lvoytek/timechime/src/sprites.c

#include <lvgl.h>

#include "sprites.h"

// I1 format: 2×lv_color32_t palette (blue,green,red,alpha) then pixel rows MSB-first.
// palette[0]=white background, palette[1]=black foreground; bit 1=arrow body.
static const uint8_t sprite_up_data[] = {
	0xFF, 0xFF, 0xFF, 0xFF, 0x00, 0x00, 0x00, 0xFF, // palette: white, black
	0x00, 0x01, 0x80, 0x00,                         // row  0: tip (2px)
	0x00, 0x03, 0xC0, 0x00,                         // row  1
	0x00, 0x07, 0xE0, 0x00,                         // row  2
	0x00, 0x0F, 0xF0, 0x00,                         // row  3
	0x00, 0x1F, 0xF8, 0x00,                         // row  4
	0x00, 0x3F, 0xFC, 0x00,                         // row  5
	0x00, 0x7F, 0xFE, 0x00,                         // row  6
	0x00, 0xFF, 0xFF, 0x00,                         // row  7
	0x01, 0xFF, 0xFF, 0x80,                         // row  8
	0x03, 0xFF, 0xFF, 0xC0,                         // row  9
	0x07, 0xFF, 0xFF, 0xE0,                         // row 10
	0x0F, 0xFF, 0xFF, 0xF0,                         // row 11
	0x1F, 0xFF, 0xFF, 0xF8,                         // row 12
	0x3F, 0xFF, 0xFF, 0xFC,                         // row 13
	0x7F, 0xFF, 0xFF, 0xFE,                         // row 14
	0xFF, 0xFF, 0xFF, 0xFF,                         // row 15: base (32px)
	0x00, 0x0F, 0xF0, 0x00,                         // row 16: stem start (8px)
	0x00, 0x0F, 0xF0, 0x00,                         // row 17
	0x00, 0x0F, 0xF0, 0x00,                         // row 18
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
	0x00, 0x03, 0xC0, 0x00,                         // row 28
	0x00, 0x01, 0x80, 0x00,                         // row 29: clapper tip (2px)
	0x00, 0x00, 0x00, 0x00,                         // row 30: empty
	0x00, 0x00, 0x00, 0x00,                         // row 31
};

// 8 teeth at N/S/E/W and four diagonal positions; center hub hole
static const uint8_t sprite_gear_data[] = {
	0xFF, 0xFF, 0xFF, 0xFF, 0x00, 0x00, 0x00, 0xFF, // palette: white, black
	0x00, 0x0F, 0xF0, 0x00,                         // row  0: N tooth (8px)
	0x00, 0x0F, 0xF0, 0x00,                         // row  1
	0x00, 0x0F, 0xF0, 0x00,                         // row  2
	0x00, 0x0F, 0xF0, 0x00,                         // row  3
	0x0F, 0x0F, 0xF0, 0xF0,                         // row  4: diagonal teeth + body
	0x0F, 0x3F, 0xFC, 0xF0,                         // row  5
	0x0F, 0xFF, 0xFF, 0xF0,                         // row  6
	0x0F, 0xFF, 0xFF, 0xF0,                         // row  7
	0x03, 0xFF, 0xFF, 0x80,                         // row  8: body (19px)
	0x07, 0xFF, 0xFF, 0xC0,                         // row  9: body (21px)
	0x07, 0xFF, 0xFF, 0xE0,                         // row 10: body (22px)
	0x0F, 0xFF, 0xFF, 0xF0,                         // row 11: body (24px)
	0xFF, 0xFC, 0x3F, 0xFF,                         // row 12: W/E teeth, center hole (4px)
	0xFF, 0xF8, 0x1F, 0xFF,                         // row 13: W/E teeth, center hole (6px)
	0xFF, 0xF0, 0x0F, 0xFF,                         // row 14: W/E teeth, center hole (8px)
	0xFF, 0xF0, 0x0F, 0xFF,                         // row 15
	0xFF, 0xF0, 0x0F, 0xFF,                         // row 16
	0xFF, 0xF0, 0x0F, 0xFF,                         // row 17
	0xFF, 0xF8, 0x1F, 0xFF,                         // row 18: W/E teeth, center hole (6px)
	0xFF, 0xFC, 0x3F, 0xFF,                         // row 19: W/E teeth, center hole (4px)
	0x0F, 0xFF, 0xFF, 0xF0,                         // row 20: body (24px)
	0x07, 0xFF, 0xFF, 0xE0,                         // row 21: body (22px)
	0x07, 0xFF, 0xFF, 0xC0,                         // row 22: body (21px)
	0x03, 0xFF, 0xFF, 0x80,                         // row 23: body (19px)
	0x0F, 0xFF, 0xFF, 0xF0,                         // row 24: diagonal teeth + body
	0x0F, 0xFF, 0xFF, 0xF0,                         // row 25
	0x0F, 0x3F, 0xFC, 0xF0,                         // row 26
	0x0F, 0x0F, 0xF0, 0xF0,                         // row 27
	0x00, 0x0F, 0xF0, 0x00,                         // row 28: S tooth (8px)
	0x00, 0x0F, 0xF0, 0x00,                         // row 29
	0x00, 0x0F, 0xF0, 0x00,                         // row 30
	0x00, 0x0F, 0xF0, 0x00,                         // row 31
};

const lv_image_dsc_t sprite_plus = {
	.header = {.magic = LV_IMAGE_HEADER_MAGIC,
		   .cf = LV_COLOR_FORMAT_I1,
		   .flags = 0,
		   .w = 32,
		   .h = 32,
		   .stride = 4},
	.data_size = sizeof(sprite_plus_data),
	.data = sprite_plus_data,
};

const lv_image_dsc_t sprite_bell = {
	.header = {.magic = LV_IMAGE_HEADER_MAGIC,
		   .cf = LV_COLOR_FORMAT_I1,
		   .flags = 0,
		   .w = 32,
		   .h = 32,
		   .stride = 4},
	.data_size = sizeof(sprite_bell_data),
	.data = sprite_bell_data,
};

const lv_image_dsc_t sprite_gear = {
	.header = {.magic = LV_IMAGE_HEADER_MAGIC,
		   .cf = LV_COLOR_FORMAT_I1,
		   .flags = 0,
		   .w = 32,
		   .h = 32,
		   .stride = 4},
	.data_size = sizeof(sprite_gear_data),
	.data = sprite_gear_data,
};

static const uint8_t sprite_sound_select_data[] = {
	0xFF, 0xFF, 0xFF, 0xFF, 0x00, 0x00, 0x00, 0xFF, // palette: white, black
	0x00, 0x00, 0x00, 0x00,                         // row  0: empty
	0x00, 0x00, 0x80, 0x00,                         // row  1: (1px)
	0x00, 0x01, 0x80, 0x00,                         // row  2: (2px)
	0x00, 0x03, 0x80, 0x20,                         // row  3: (4px)
	0x00, 0x07, 0x80, 0x10,                         // row  4: (5px)
	0x00, 0x0F, 0x80, 0x10,                         // row  5: (6px)
	0x00, 0x1F, 0x80, 0x08,                         // row  6: (7px)
	0x00, 0x3F, 0x80, 0x08,                         // row  7: (8px)
	0x00, 0x7F, 0x81, 0x04,                         // row  8: (10px)
	0x00, 0xFF, 0x81, 0x04,                         // row  9: (11px)
	0xFF, 0xFF, 0x80, 0x84,                         // row 10: (19px)
	0xFF, 0xFF, 0x90, 0x84,                         // row 11: (20px)
	0xFF, 0xFF, 0x88, 0x42,                         // row 12: (20px)
	0xFF, 0xFF, 0x88, 0x42,                         // row 13: (20px)
	0xFF, 0xFF, 0x84, 0x42,                         // row 14: (20px)
	0xFF, 0xFF, 0x84, 0x22,                         // row 15: (20px)
	0xFF, 0xFF, 0x84, 0x22,                         // row 16: (20px)
	0xFF, 0xFF, 0x84, 0x22,                         // row 17: (20px)
	0xFF, 0xFF, 0x88, 0x42,                         // row 18: (20px)
	0xFF, 0xFF, 0x88, 0x42,                         // row 19: (20px)
	0xFF, 0xFF, 0x90, 0x44,                         // row 20: (20px)
	0xFF, 0xFF, 0x80, 0x84,                         // row 21: (19px)
	0x00, 0xFF, 0x80, 0x84,                         // row 22: (11px)
	0x00, 0x7F, 0x81, 0x08,                         // row 23: (10px)
	0x00, 0x3F, 0x81, 0x08,                         // row 24: (9px)
	0x00, 0x1F, 0x80, 0x10,                         // row 25: (7px)
	0x00, 0x0F, 0x80, 0x10,                         // row 26: (6px)
	0x00, 0x07, 0x80, 0x20,                         // row 27: (5px)
	0x00, 0x03, 0x80, 0x20,                         // row 28: (4px)
	0x00, 0x01, 0x80, 0x00,                         // row 29: (2px)
	0x00, 0x00, 0x80, 0x00,                         // row 30: (1px)
	0x00, 0x00, 0x00, 0x00,                         // row 31: empty
};

const lv_image_dsc_t sprite_sound_select = {
	.header = {.magic = LV_IMAGE_HEADER_MAGIC,
		   .cf = LV_COLOR_FORMAT_I1,
		   .flags = 0,
		   .w = 32,
		   .h = 32,
		   .stride = 4},
	.data_size = sizeof(sprite_sound_select_data),
	.data = sprite_sound_select_data,
};

static const uint8_t sprite_toggle_on_data[] = {
	0xFF, 0xFF, 0xFF, 0xFF, 0x00, 0x00, 0x00, 0xFF, // palette: white, black
	0x00, 0x00, 0x00, 0x00,                         // row  0: empty
	0x00, 0x00, 0x00, 0x00,                         // row  1: empty
	0x00, 0x00, 0x00, 0x00,                         // row  2: empty
	0x00, 0x00, 0x00, 0x00,                         // row  3: empty
	0x00, 0x00, 0x00, 0x00,                         // row  4: empty
	0x00, 0x00, 0x00, 0x00,                         // row  5: empty
	0x00, 0x00, 0x00, 0x00,                         // row  6: empty
	0x0F, 0xFF, 0xFF, 0xF0,                         // row  7: (24px)
	0x1F, 0xFF, 0xFF, 0xF8,                         // row  8: (26px)
	0x3F, 0xFF, 0xF8, 0x3C,                         // row  9: (23px)
	0x7F, 0xFF, 0xF0, 0x1E,                         // row 10: (23px)
	0xFF, 0xFF, 0xE0, 0x0F,                         // row 11: (23px)
	0xFF, 0xFF, 0xC0, 0x07,                         // row 12: (21px)
	0xFF, 0xFF, 0x80, 0x03,                         // row 13: (19px)
	0xFF, 0xFF, 0x80, 0x03,                         // row 14: (19px)
	0xFF, 0xFF, 0x80, 0x03,                         // row 15: (19px)
	0xFF, 0xFF, 0x80, 0x03,                         // row 16: (19px)
	0xFF, 0xFF, 0x80, 0x03,                         // row 17: (19px)
	0xFF, 0xFF, 0xC0, 0x07,                         // row 18: (21px)
	0xFF, 0xFF, 0xE0, 0x0F,                         // row 19: (23px)
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
	0x03, 0x66, 0x66, 0xC0,                         // row 28: (12px)
	0x03, 0xFF, 0xFF, 0xC0,                         // row 29: (20px)
	0x03, 0xFF, 0xFF, 0xC0,                         // row 30: (20px)
	0x03, 0xFF, 0xFF, 0xC0,                         // row 31: (20px)
};

static const uint8_t sprite_time_data[] = {
	0xFF, 0xFF, 0xFF, 0xFF, 0x00, 0x00, 0x00, 0xFF, // palette: white, black
	0x00, 0x3F, 0xFC, 0x00,                         // row  0: (12px)
	0x00, 0xFF, 0xFF, 0x00,                         // row  1: (16px)
	0x01, 0xF8, 0x1F, 0x80,                         // row  2: (12px)
	0x07, 0xC1, 0x03, 0xE0,                         // row  3: (11px)
	0x0F, 0x03, 0x80, 0xF0,                         // row  4: (11px)
	0x1E, 0x03, 0x80, 0x78,                         // row  5: (11px)
	0x1C, 0x03, 0x80, 0x38,                         // row  6: (9px)
	0x38, 0x03, 0x80, 0x1C,                         // row  7: (9px)
	0x70, 0x03, 0x80, 0x0E,                         // row  8: (9px)
	0x70, 0x03, 0x80, 0x0E,                         // row  9: (9px)
	0xE0, 0x03, 0x80, 0x07,                         // row 10: (9px)
	0xE0, 0x03, 0x80, 0x07,                         // row 11: (9px)
	0xE0, 0x03, 0x80, 0x07,                         // row 12: (9px)
	0xC0, 0x03, 0x80, 0x03,                         // row 13: (7px)
	0xC0, 0x03, 0x80, 0x03,                         // row 14: (7px)
	0xC0, 0x03, 0x80, 0x03,                         // row 15: (7px)
	0xC0, 0x03, 0x80, 0x03,                         // row 16: (7px)
	0xC0, 0x03, 0xC0, 0x03,                         // row 17: (8px)
	0xC0, 0x01, 0xF0, 0x03,                         // row 18: (9px)
	0xE0, 0x00, 0xFC, 0x07,                         // row 19: (12px)
	0xE0, 0x00, 0x3F, 0x07,                         // row 20: (12px)
	0xE0, 0x00, 0x0F, 0xC7,                         // row 21: (12px)
	0x70, 0x00, 0x03, 0xEE,                         // row 22: (11px)
	0x70, 0x00, 0x00, 0xCE,                         // row 23: (8px)
	0x38, 0x00, 0x00, 0x1C,                         // row 24: (6px)
	0x1C, 0x00, 0x00, 0x38,                         // row 25: (6px)
	0x1E, 0x00, 0x00, 0x78,                         // row 26: (8px)
	0x0F, 0x00, 0x00, 0xF0,                         // row 27: (8px)
	0x07, 0xC0, 0x03, 0xE0,                         // row 28: (10px)
	0x01, 0xF8, 0x1F, 0x80,                         // row 29: (12px)
	0x00, 0xFF, 0xFF, 0x00,                         // row 30: (16px)
	0x00, 0x3F, 0xFC, 0x00,                         // row 31: (12px)
};

const lv_image_dsc_t sprite_time = {
	.header = {.magic = LV_IMAGE_HEADER_MAGIC,
		   .cf = LV_COLOR_FORMAT_I1,
		   .flags = 0,
		   .w = 32,
		   .h = 32,
		   .stride = 4},
	.data_size = sizeof(sprite_time_data),
	.data = sprite_time_data,
};

const lv_image_dsc_t sprite_trash = {
	.header = {.magic = LV_IMAGE_HEADER_MAGIC,
		   .cf = LV_COLOR_FORMAT_I1,
		   .flags = 0,
		   .w = 32,
		   .h = 32,
		   .stride = 4},
	.data_size = sizeof(sprite_trash_data),
	.data = sprite_trash_data,
};

static const uint8_t sprite_confirm_data[] = {
	0xFF, 0xFF, 0xFF, 0xFF, 0x00, 0x00, 0x00, 0xFF, // palette: white, black
	0x00, 0x00, 0x00, 0x00,                         // row  0: empty
	0x00, 0x00, 0x00, 0x00,                         // row  1: empty
	0x00, 0x00, 0x00, 0x00,                         // row  2: empty
	0x00, 0x00, 0x00, 0x03,                         // row  3: (2px)
	0x00, 0x00, 0x00, 0x1F,                         // row  4: (5px)
	0x00, 0x00, 0x00, 0x7E,                         // row  5: (6px)
	0x00, 0x00, 0x00, 0xFC,                         // row  6: (6px)
	0x00, 0x00, 0x01, 0xF8,                         // row  7: (6px)
	0x00, 0x00, 0x03, 0xF0,                         // row  8: (6px)
	0x00, 0x00, 0x07, 0xE0,                         // row  9: (6px)
	0x00, 0x00, 0x0F, 0xC0,                         // row 10: (6px)
	0x00, 0x00, 0x1F, 0x80,                         // row 11: (6px)
	0x00, 0x00, 0x3F, 0x00,                         // row 12: (6px)
	0x00, 0x00, 0x7E, 0x00,                         // row 13: (6px)
	0xC0, 0x00, 0xFC, 0x00,                         // row 14: (8px)
	0xF0, 0x00, 0xF8, 0x00,                         // row 15: (9px)
	0xFC, 0x01, 0xF8, 0x00,                         // row 16: (12px)
	0xFE, 0x01, 0xF0, 0x00,                         // row 17: (12px)
	0x7F, 0x83, 0xE0, 0x00,                         // row 18: (13px)
	0x3F, 0xC3, 0xC0, 0x00,                         // row 19: (12px)
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
};

const lv_image_dsc_t sprite_gpssearch = {
	.header = {.magic = LV_IMAGE_HEADER_MAGIC,
		   .cf = LV_COLOR_FORMAT_I1,
		   .flags = 0,
		   .w = 200,
		   .h = 200,
		   .stride = 25},
	.data_size = sizeof(sprite_gpssearch_data),
	.data = sprite_gpssearch_data,
};
