lvoytek/timechime/src/sprites.h

#ifndef TIMECHIME_SPRITES_H
#define TIMECHIME_SPRITES_H

#include <lvgl.h>

extern const lv_image_dsc_t sprite_up;
extern const lv_image_dsc_t sprite_down;
extern const lv_image_dsc_t sprite_plus;
extern const lv_image_dsc_t sprite_bell;
extern const lv_image_dsc_t sprite_gear;
extern const lv_image_dsc_t sprite_sound_select;
extern const lv_image_dsc_t sprite_toggle_on;
extern const lv_image_dsc_t sprite_toggle_off;
extern const lv_image_dsc_t sprite_time;
extern const lv_image_dsc_t sprite_trash;
extern const lv_image_dsc_t sprite_confirm;
extern const lv_image_dsc_t sprite_back;
extern const lv_image_dsc_t sprite_gpssearch;

#endif
